kt314-sh/MTL-2/03-pic/01.jpg

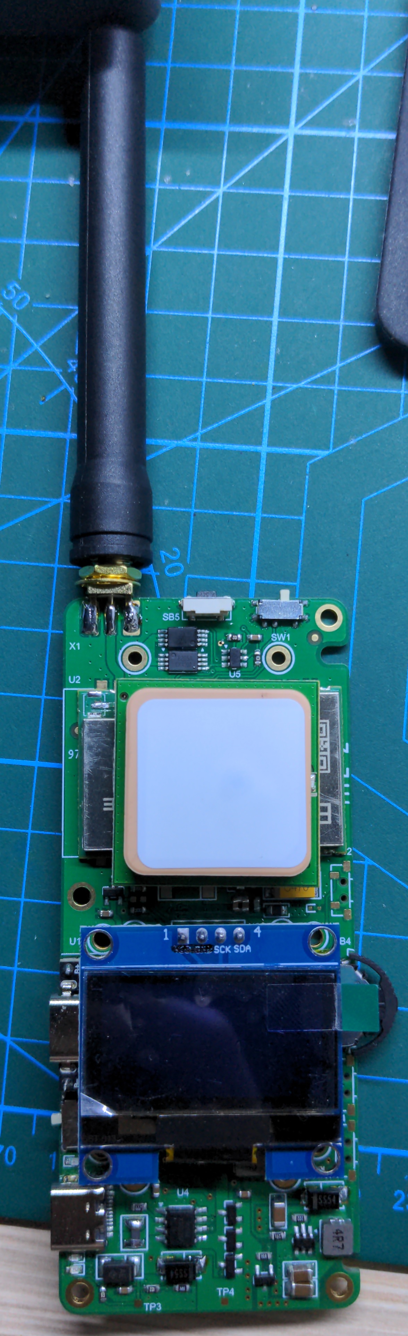
03-pic/01.jpg
