kt314-sh/MTL-2/03-pic/02.jpg

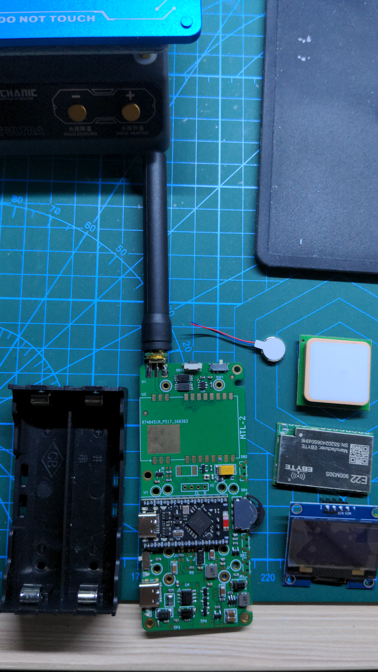
03-pic/02.jpg
