kt314-sh/MTL-2/03-pic/06-Case-ver1.jpg

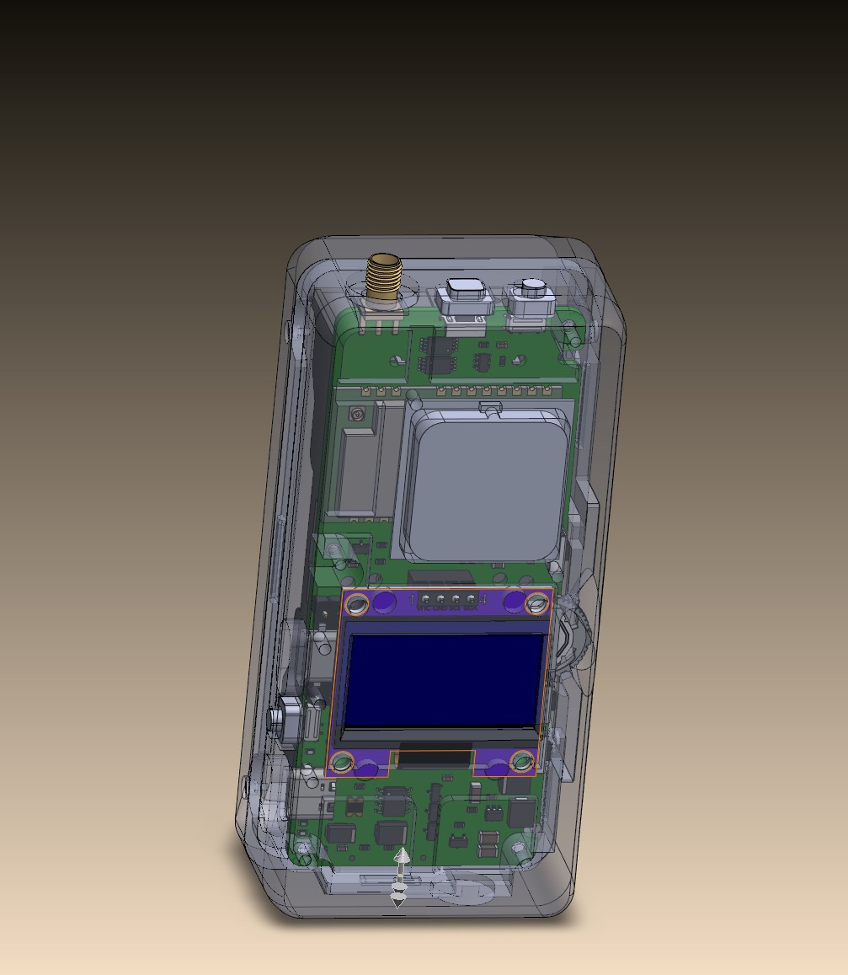
03-pic/06-Case-ver1.jpg
