kt314-sh/MTL-2/03-pic/07-Case-ver1-04.jpg

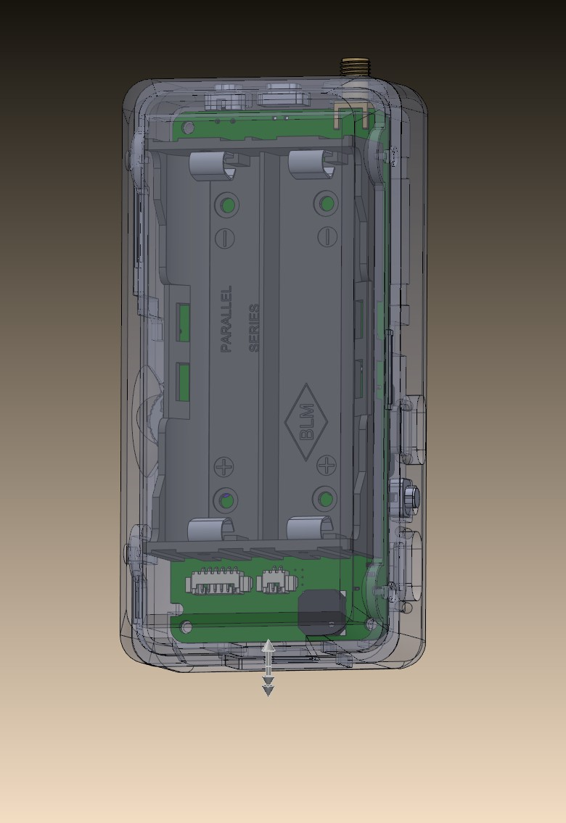
03-pic/07-Case-ver1-04.jpg
