kt314-sh/MTL-2/03-pic/09.jpg

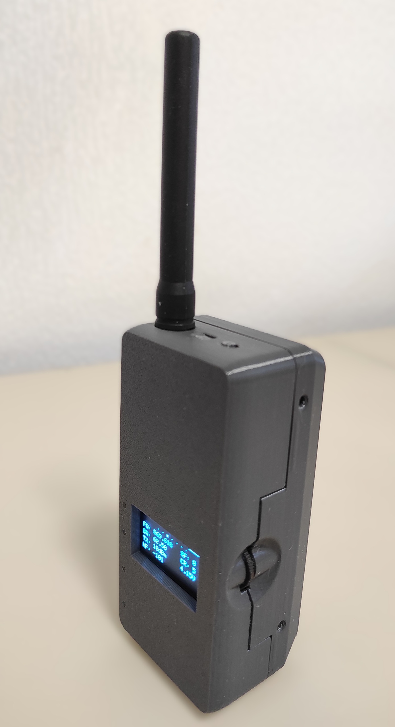
03-pic/09.jpg
