kt314-sh/MTL-2/03-pic/e22-2.png

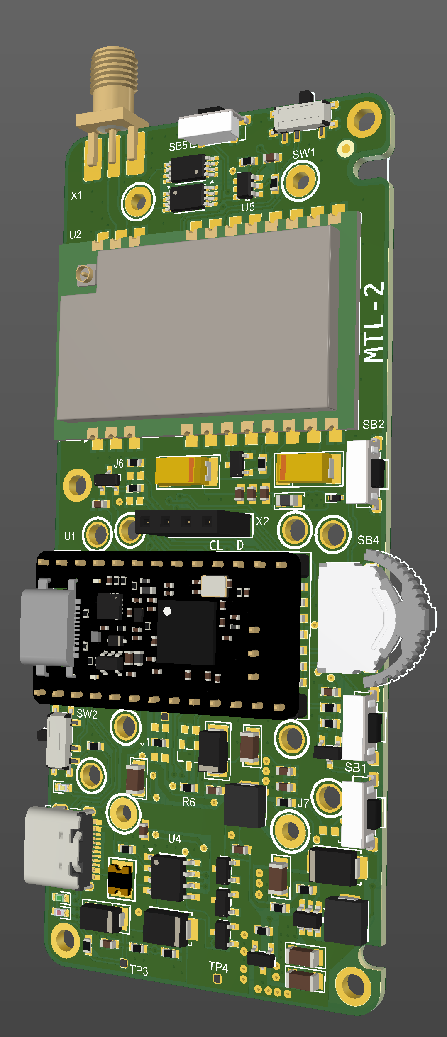
03-pic/e22-2.png
